msxmatt/bs/rev_a/documents/specs/Harwin/M22-532.pdf

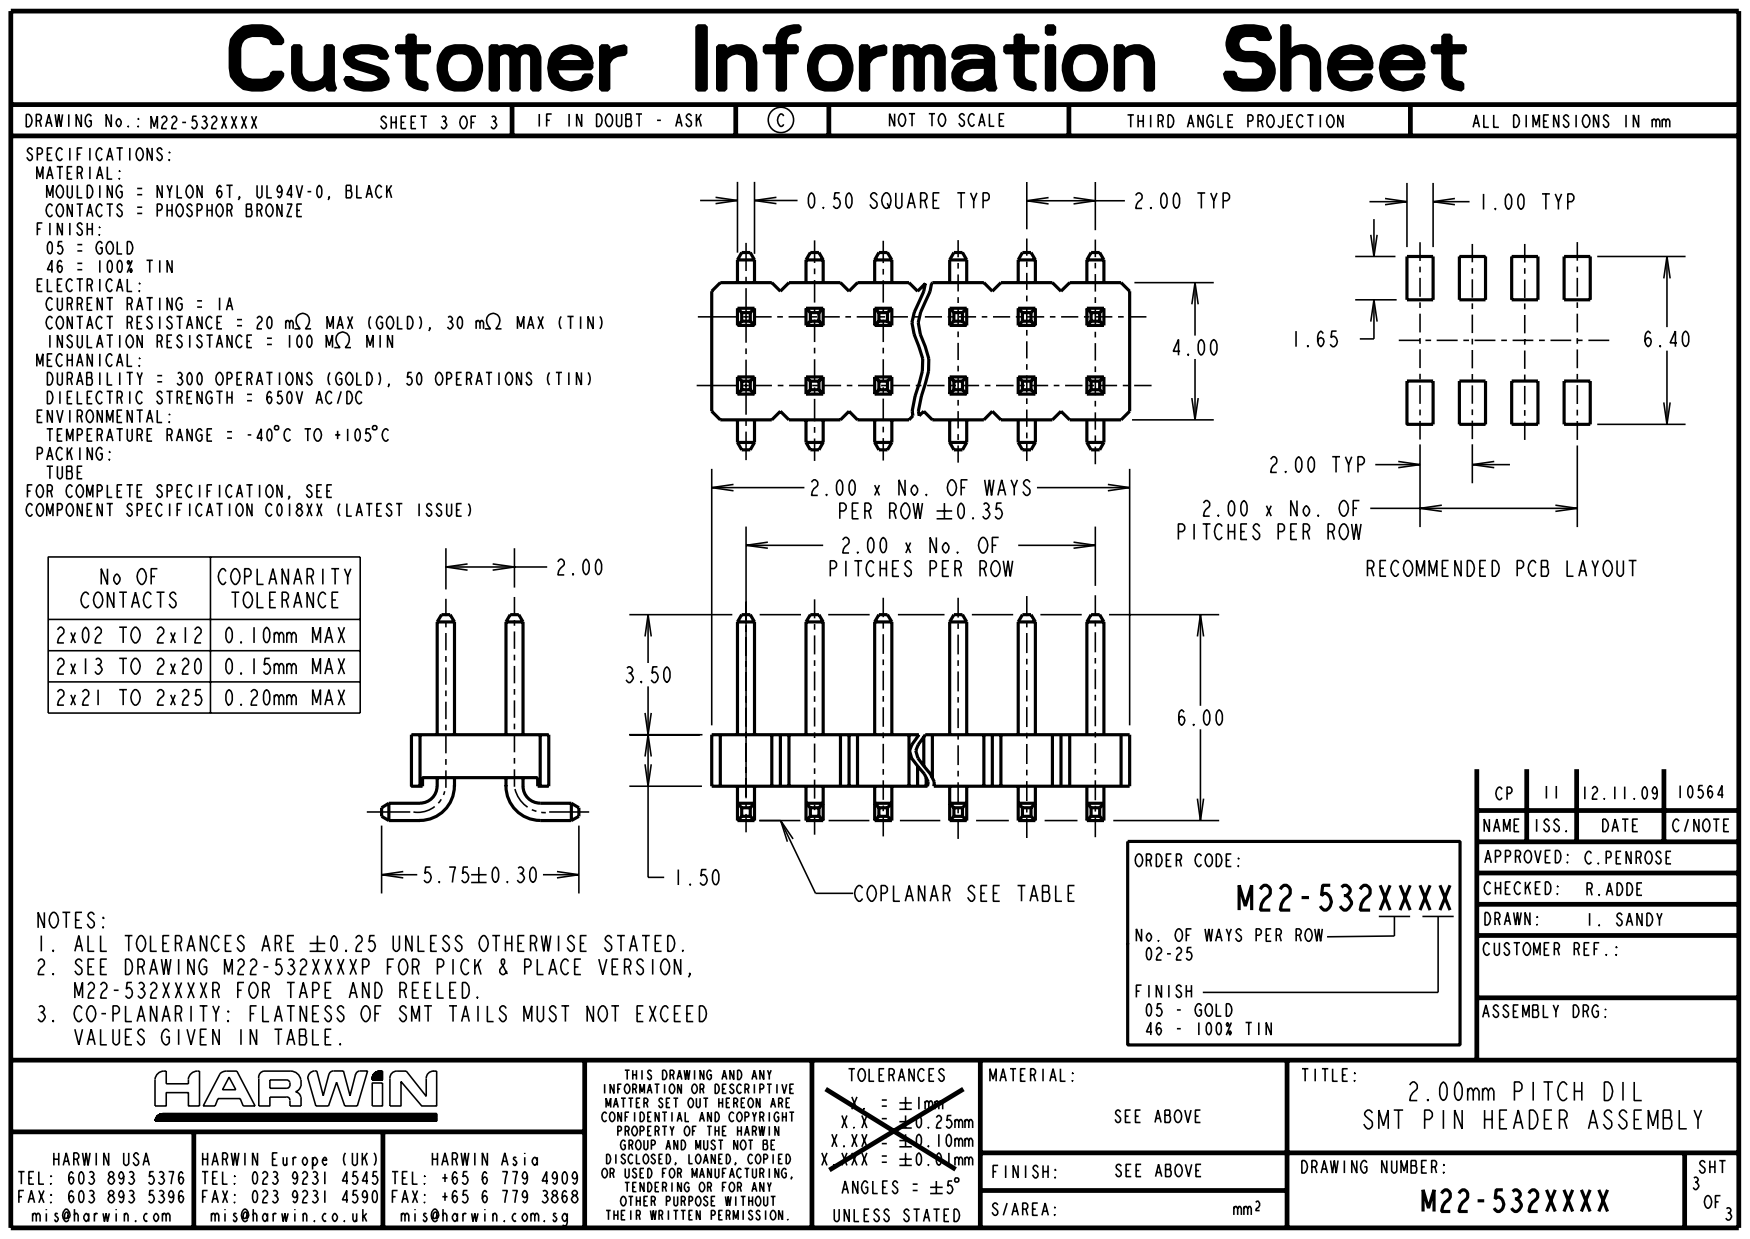
[picture p10: page 1]
