msxmatt/bs/rev_a/documents/specs/TE/FSMIJM61AB04.pdf

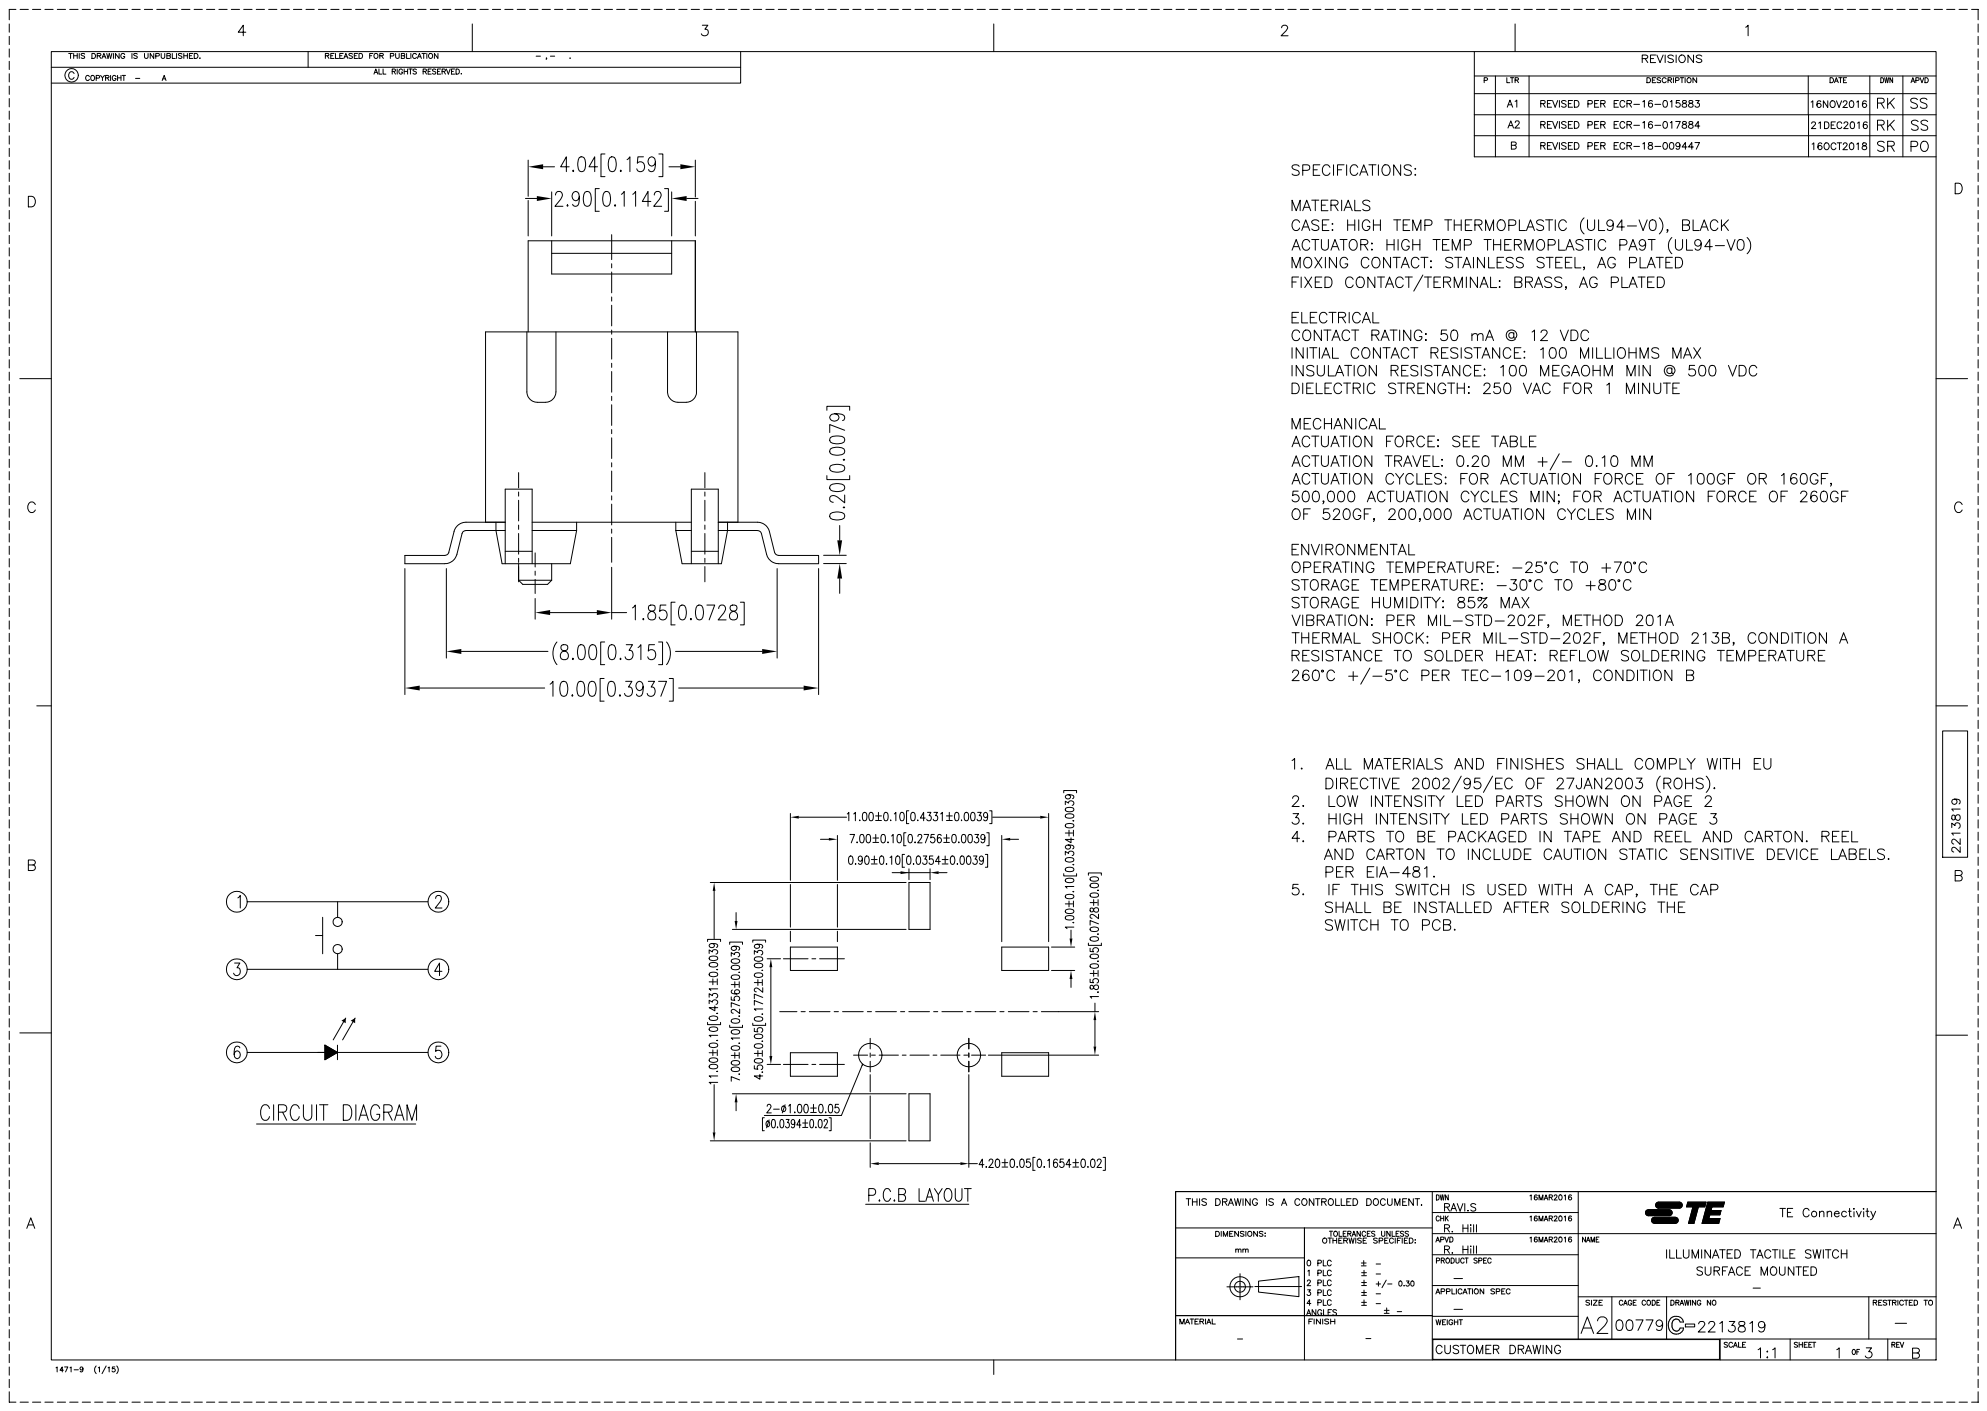
[picture p11: page 1]

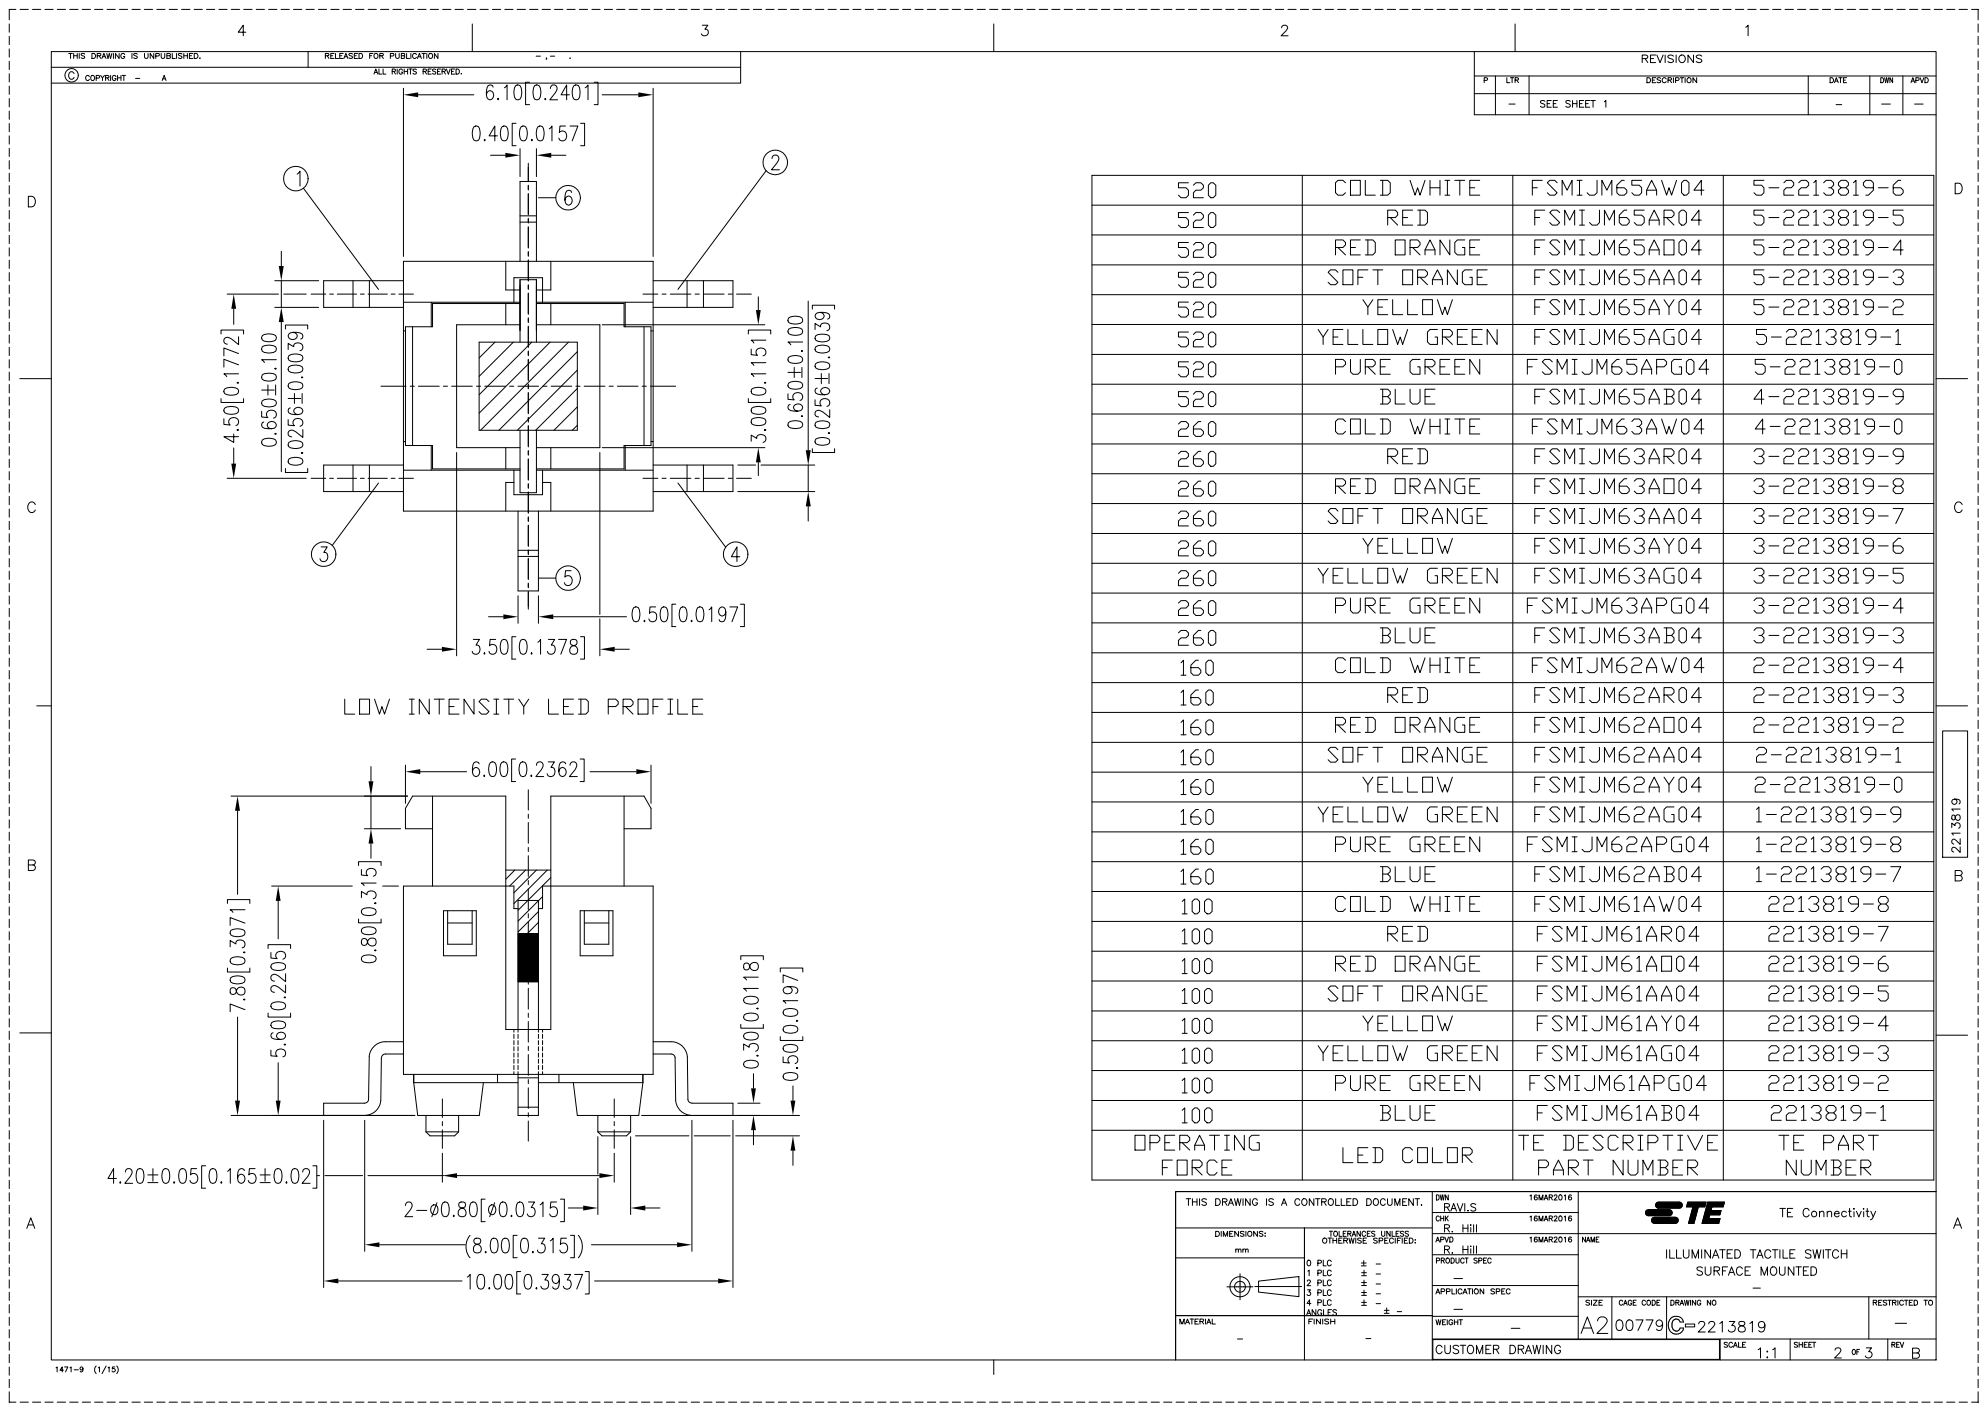
[picture p12: page 2]

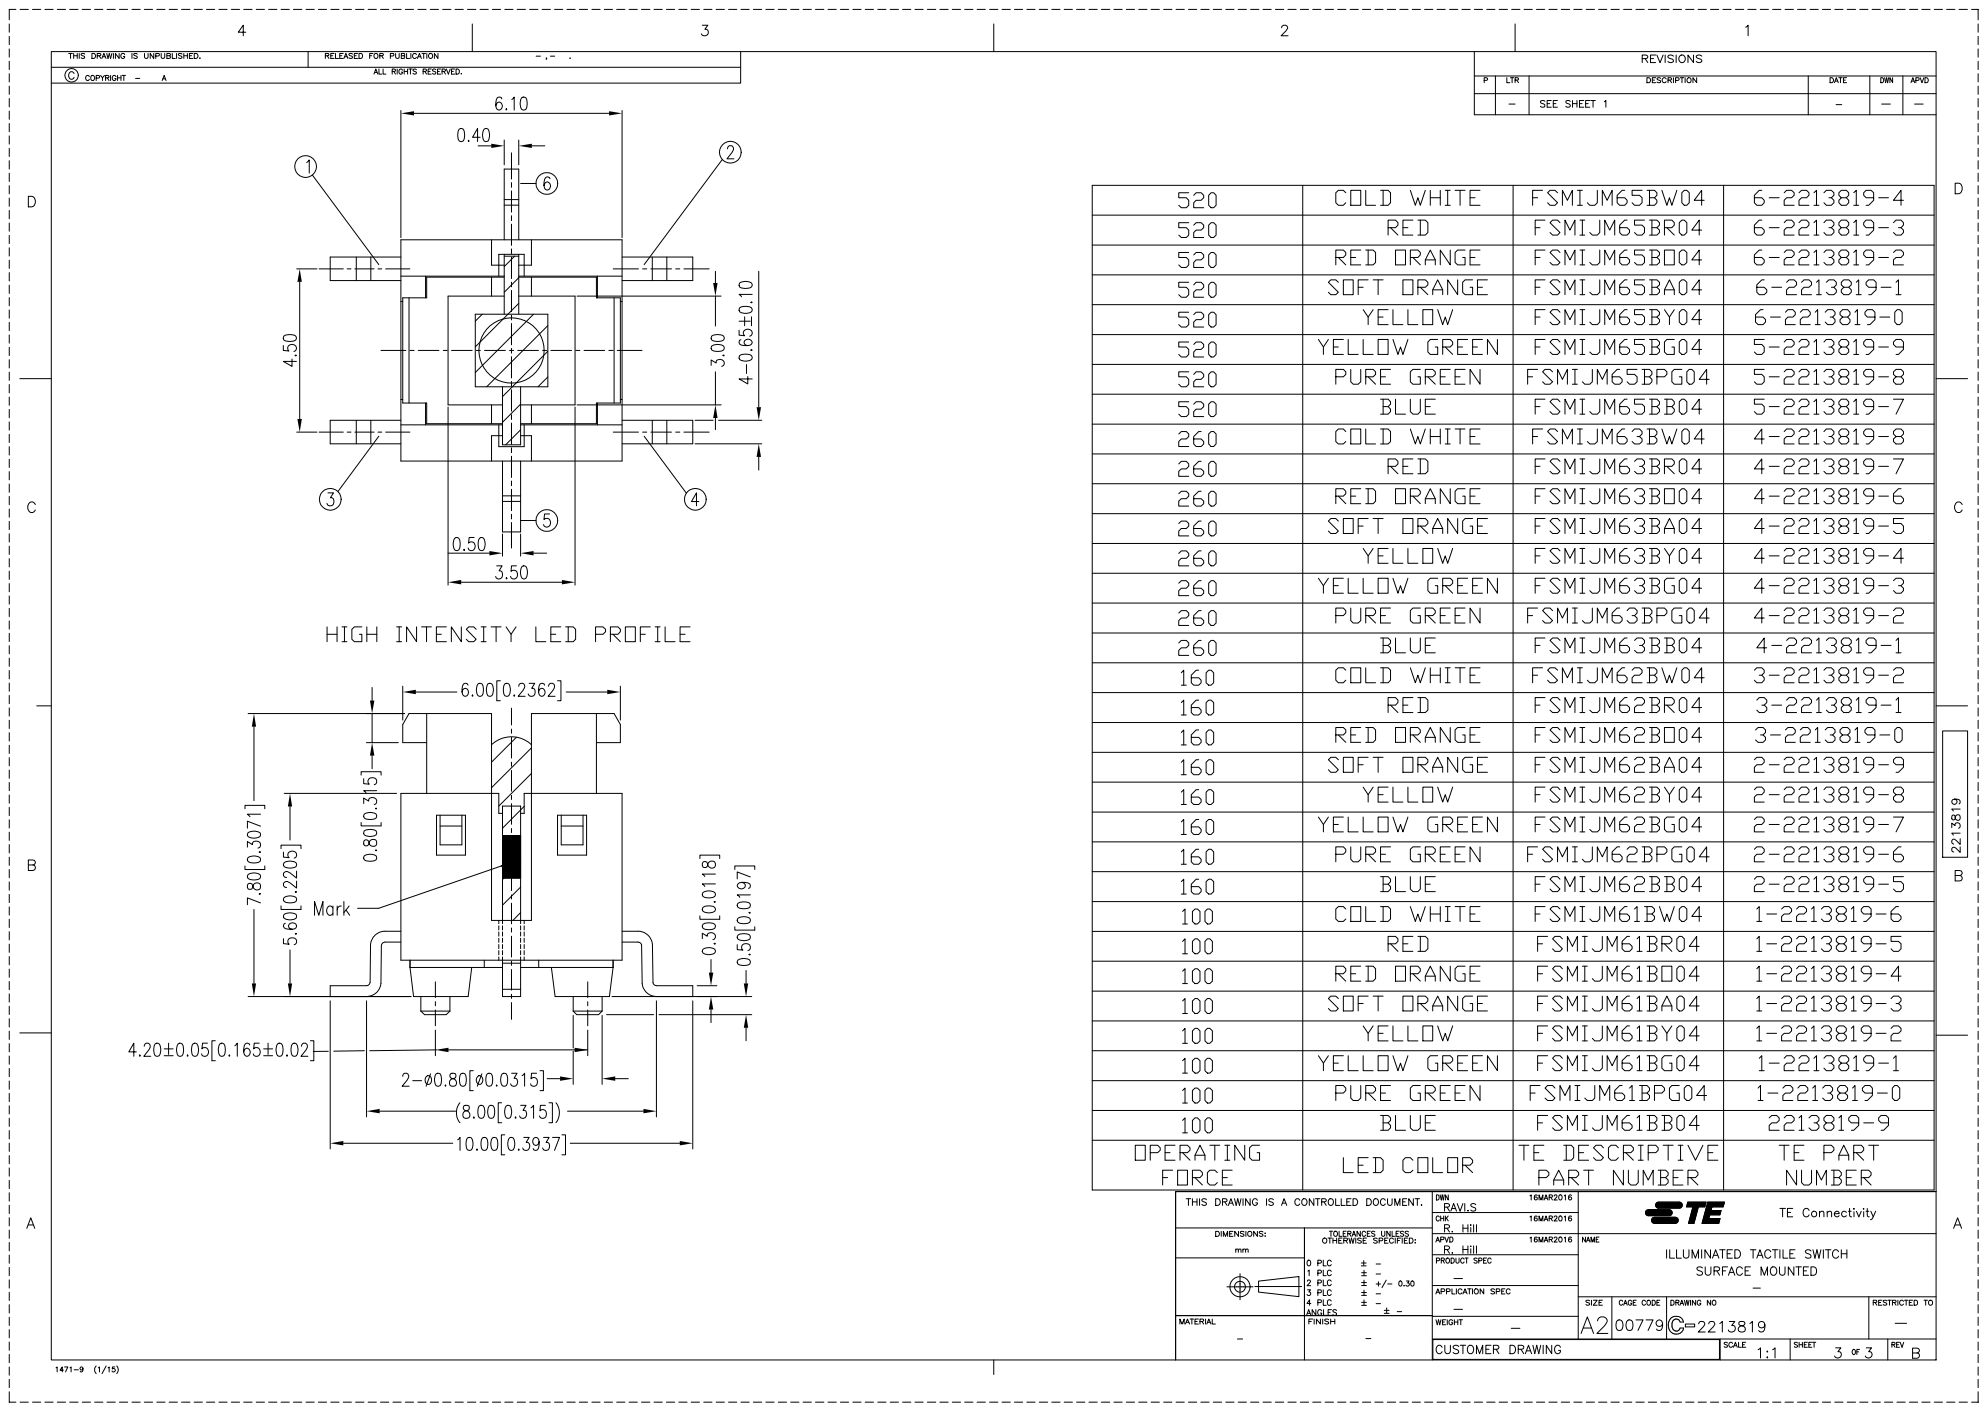
[picture p13: page 3]
