msxmatt/bs/rev_a/release/bs_1.0.5/bs.PDF

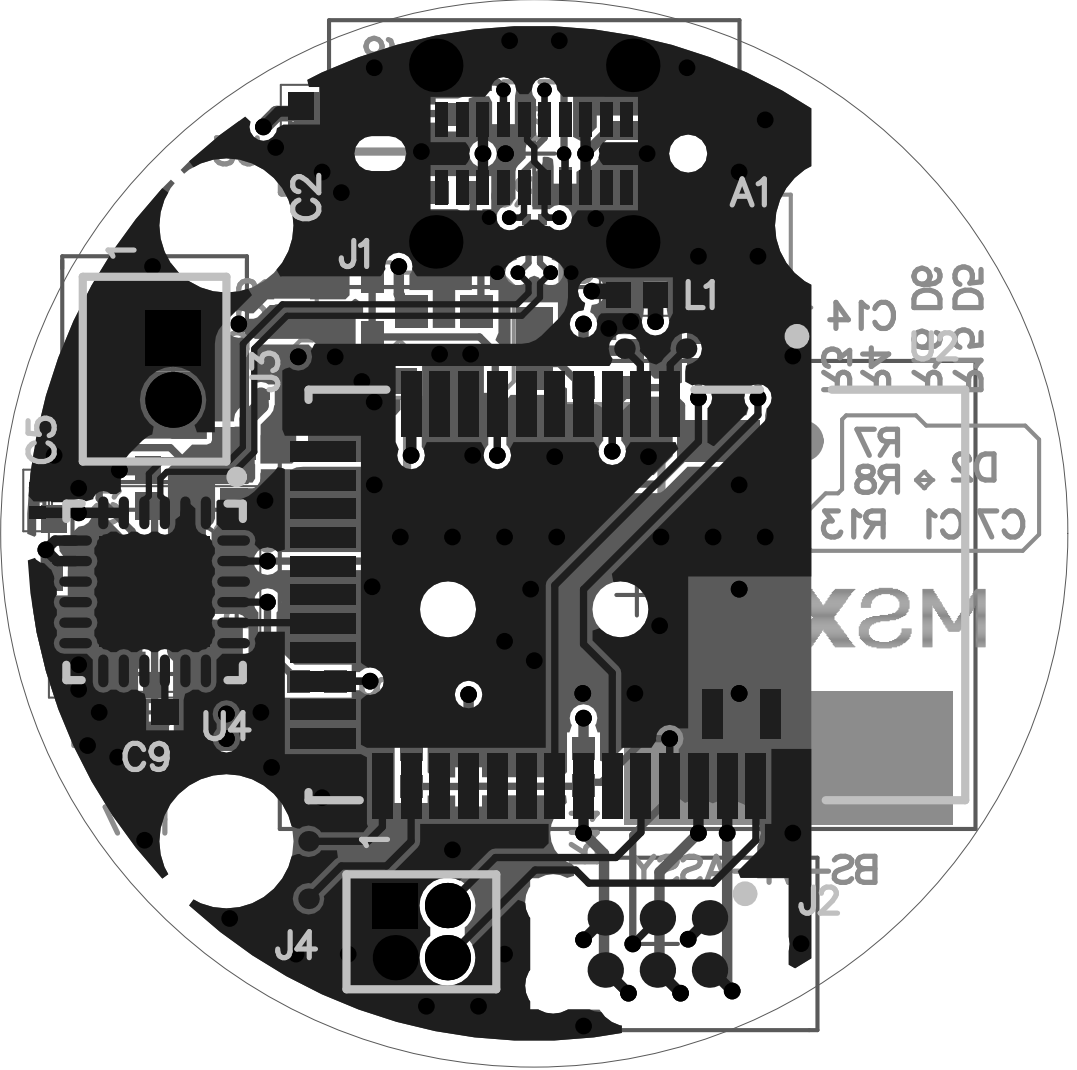
[picture p14: page 1]

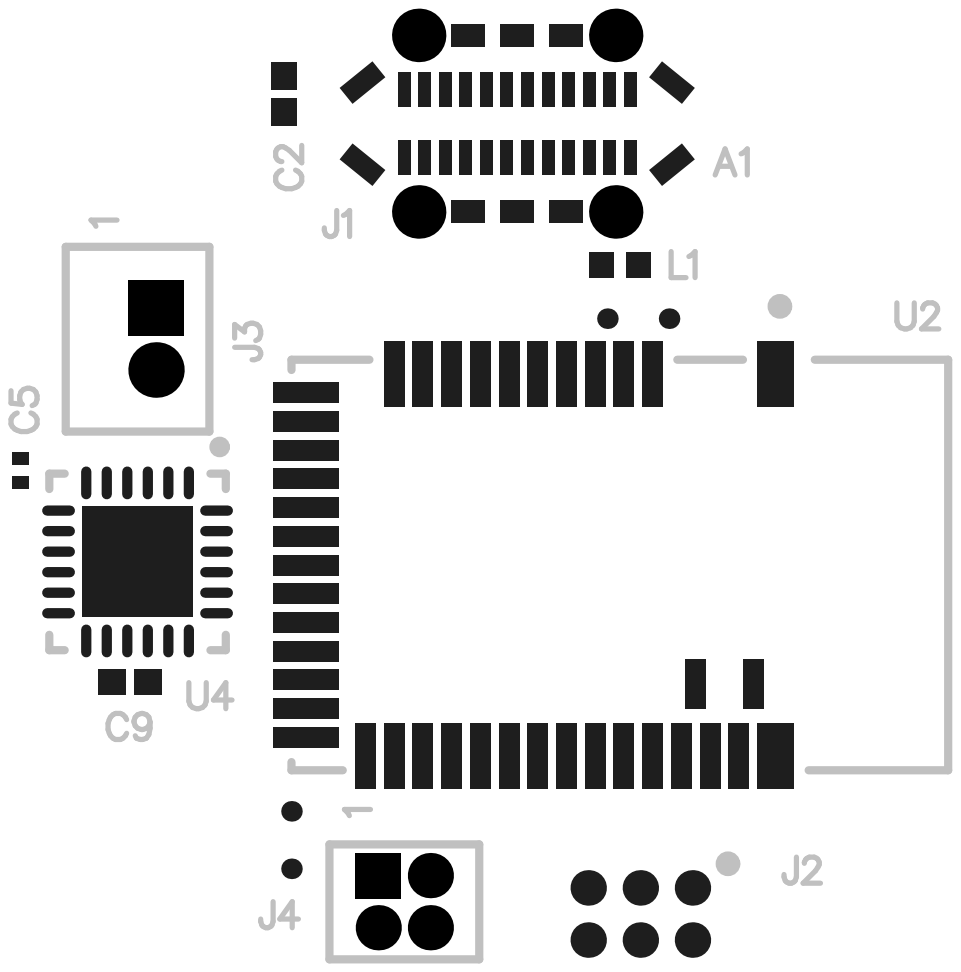
[picture p15: page 2]

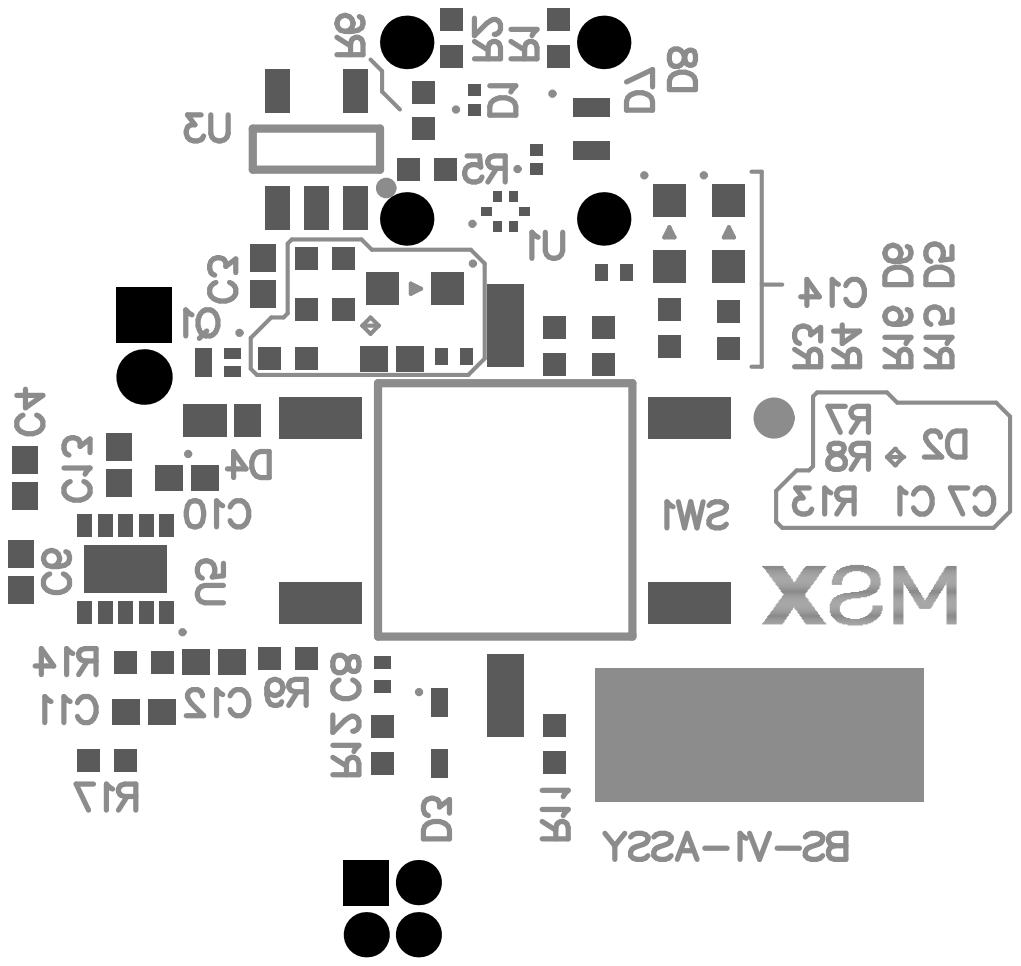
[picture p16: page 3]

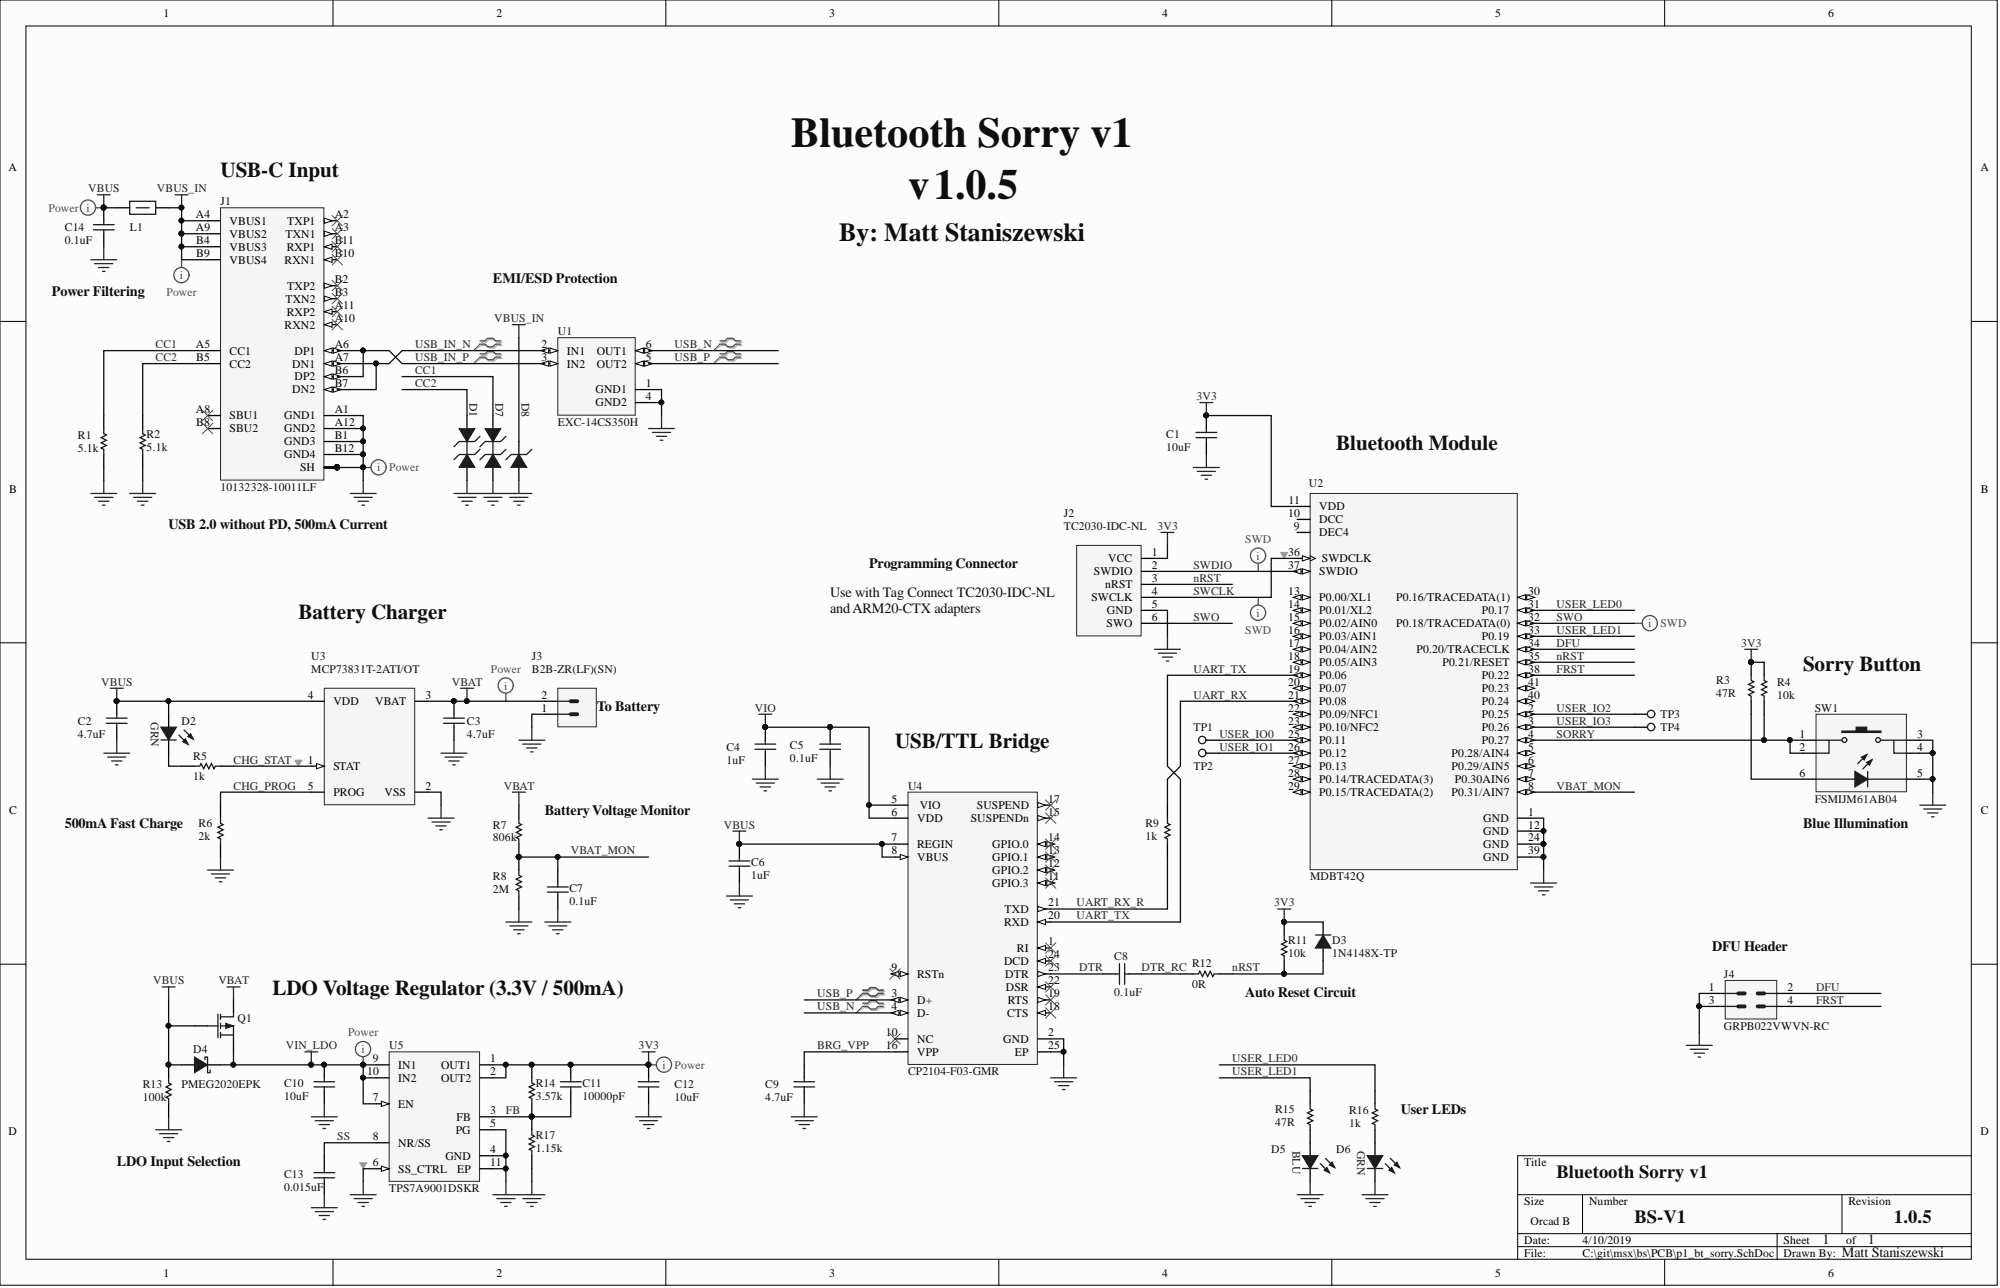
[picture p17: page 4]
