msxmatt/bs/rev_a/documents/simulation/vbus_in_filter.asc

C1: cap; 0.1µ
U1: BLM15PX601SN1
V1: voltage; SINE(5 1 100E6 0 0 0 1E9); AC 1
Named nets: 0, VBUS_IN, VBUS
.tran 0 100n 0 1n
